PierreBanwarth/MIDI-Concertina/Grille métal/documents imprimeur/jmkpoflmhifpepfo.png

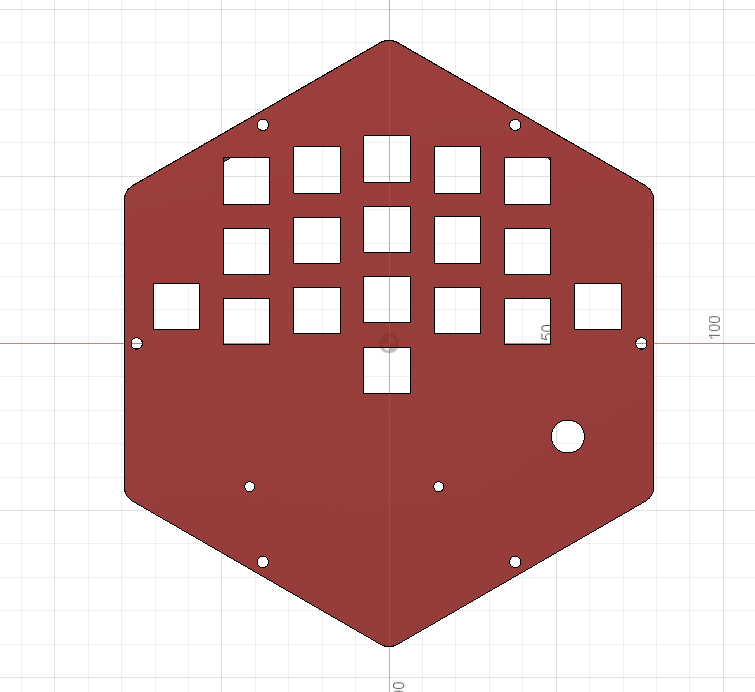
Grille métal/documents imprimeur/jmkpoflmhifpepfo.png
